Diepzeevogel/iMac-G3-replacement-parts/Mounts/SFX PSU to VESA/PSU1.stl

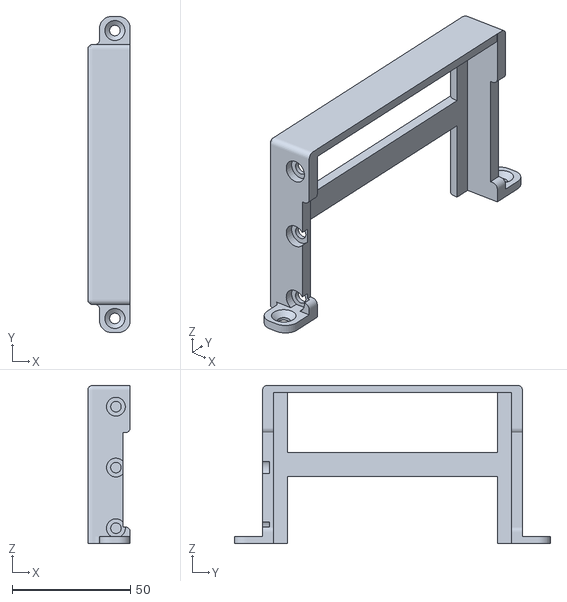
[picture p15: CAD file, 2019-09-14]
Mounts/SFX PSU to VESA/PSU1.stl
18.0 x 133.9 x 67.0
