Diepzeevogel/iMac-G3-replacement-parts/Bezel/BOTTOM_LEFT.stl

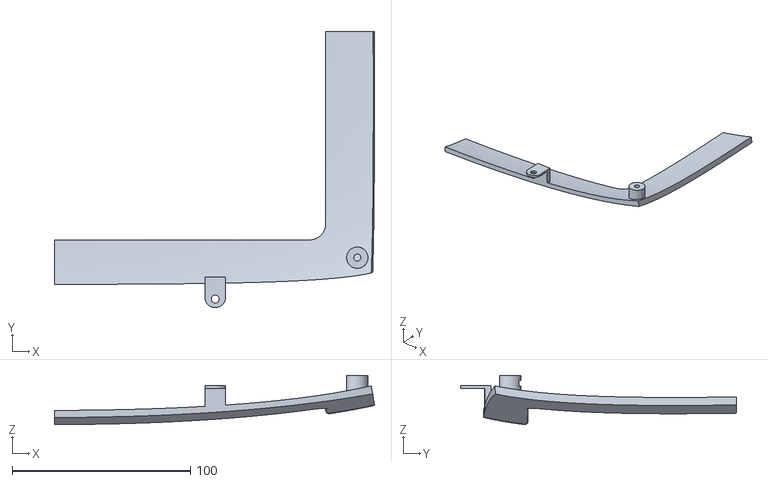
[picture p16: CAD file, 2019-07-27]
Bezel/BOTTOM_LEFT.stl
179.7 x 155.0 x 27.6
