Diepzeevogel/iMac-G3-replacement-parts/IO/Mount_Cutouts.stl

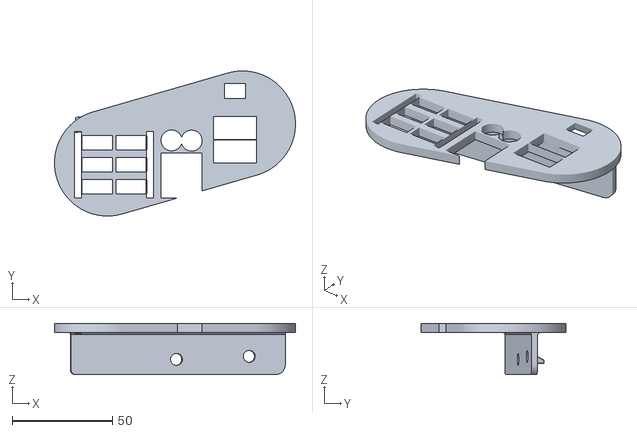
[picture p17: CAD file, 2019-09-03]
IO/Mount_Cutouts.stl
120.3 x 72.4 x 25.6
