Diepzeevogel/iMac-G3-replacement-parts/Mounts/200mm fan/fan_mount_btm.stl

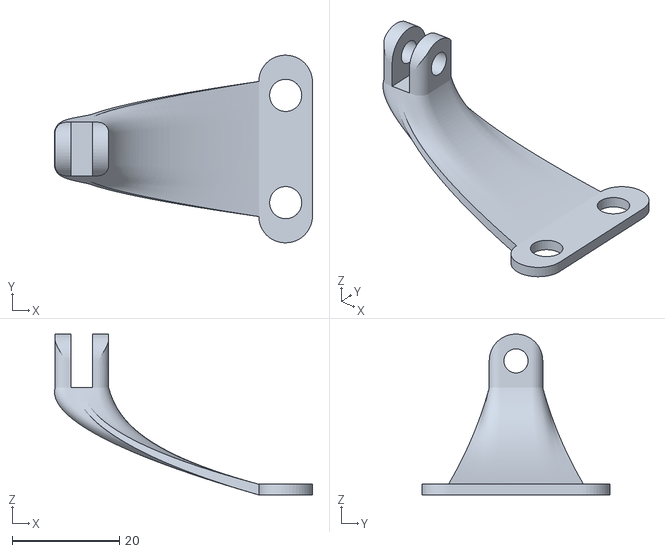
[picture p18: CAD file, 2019-09-14]
Mounts/200mm fan/fan_mount_btm.stl
48.1 x 35.0 x 30.0
