Diepzeevogel/iMac-G3-replacement-parts/Mounts/GPU/GPU protection.stl

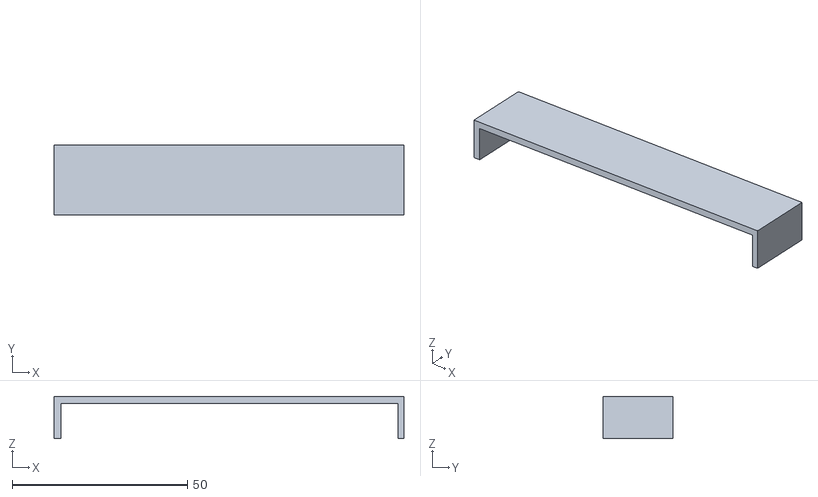
[picture p19: CAD file, 2019-09-14]
Mounts/GPU/GPU protection.stl
99.7 x 20.0 x 12.0
