Diepzeevogel/iMac-G3-replacement-parts/Mounts/SFX PSU to VESA/VESA1.stl

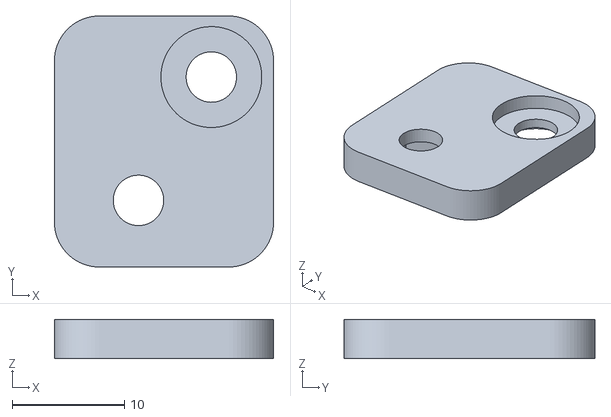
[picture p20: CAD file, 2019-09-14]
Mounts/SFX PSU to VESA/VESA1.stl
19.6 x 22.4 x 3.50
