Diepzeevogel/iMac-G3-replacement-parts/IO/IO Shield_cutouts.stl

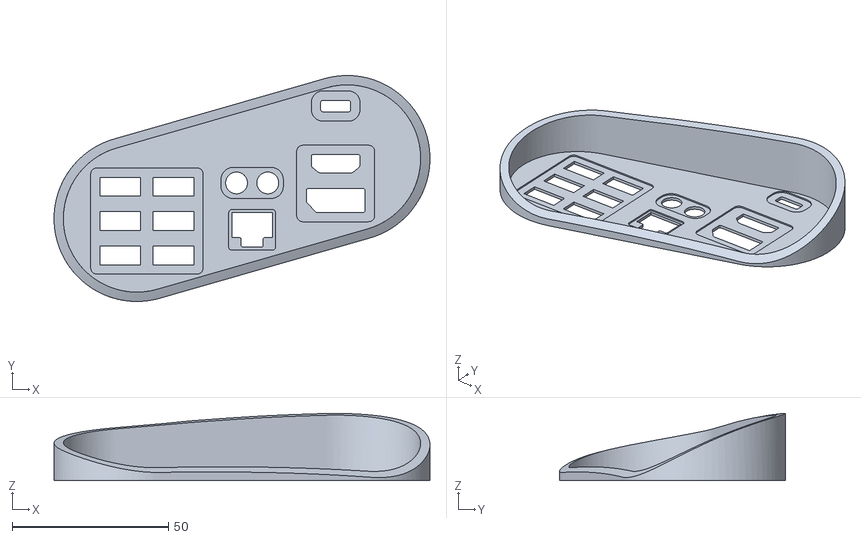
[picture p21: CAD file, 2019-09-03]
IO/IO Shield_cutouts.stl
120.3 x 72.3 x 21.5
