Diepzeevogel/iMac-G3-replacement-parts/Bezel/BOTTOM_RIGHT.stl

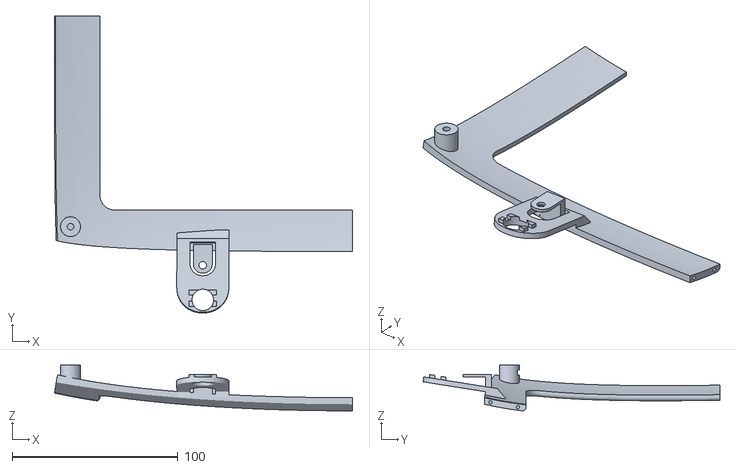
[picture p22: CAD file, 2019-07-27]
Bezel/BOTTOM_RIGHT.stl
179.7 x 179.0 x 27.6
