Diepzeevogel/iMac-G3-replacement-parts/Mounts/SFX PSU to VESA/VESA3.stl

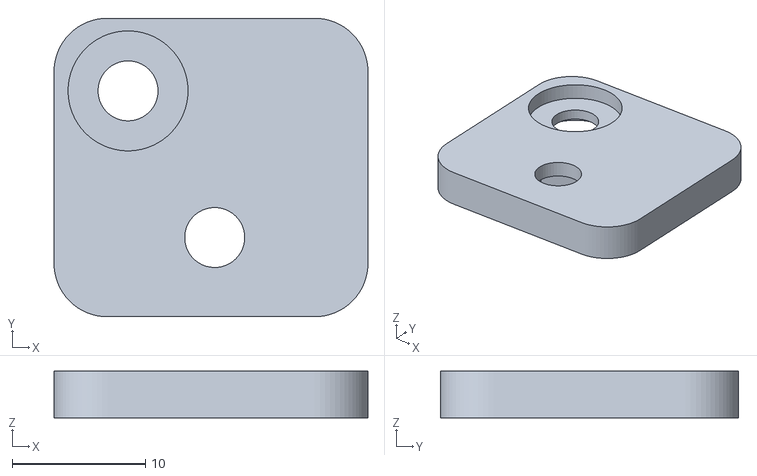
[picture p23: CAD file, 2019-09-03]
Mounts/SFX PSU to VESA/VESA3.stl
23.6 x 22.4 x 3.50
